ThaumicMekanism/ChemE-Car-Electrical-Team-2018-2019/Box/Images/analog digital.jpg

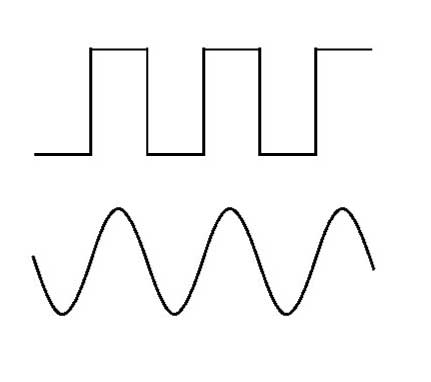
Box/Images/analog digital.jpg
