ThaumicMekanism/ChemE-Car-Electrical-Team-2018-2019/Box/Images/brain.jpg

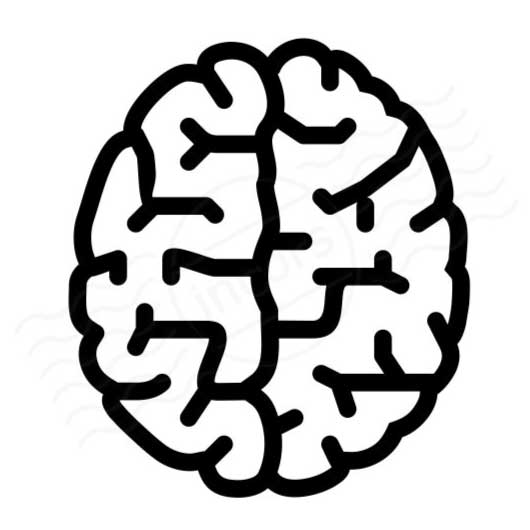
Box/Images/brain.jpg
