ThaumicMekanism/ChemE-Car-Electrical-Team-2018-2019/New Motor Control/proj-bjt.png

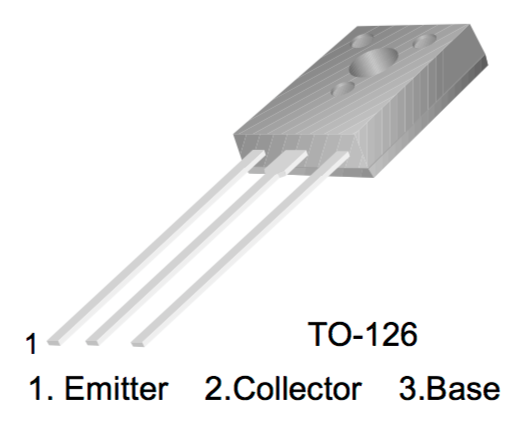
New Motor Control/proj-bjt.png
