ThaumicMekanism/ChemE-Car-Electrical-Team-2018-2019/New Motor Control/proj-motor-driver.png

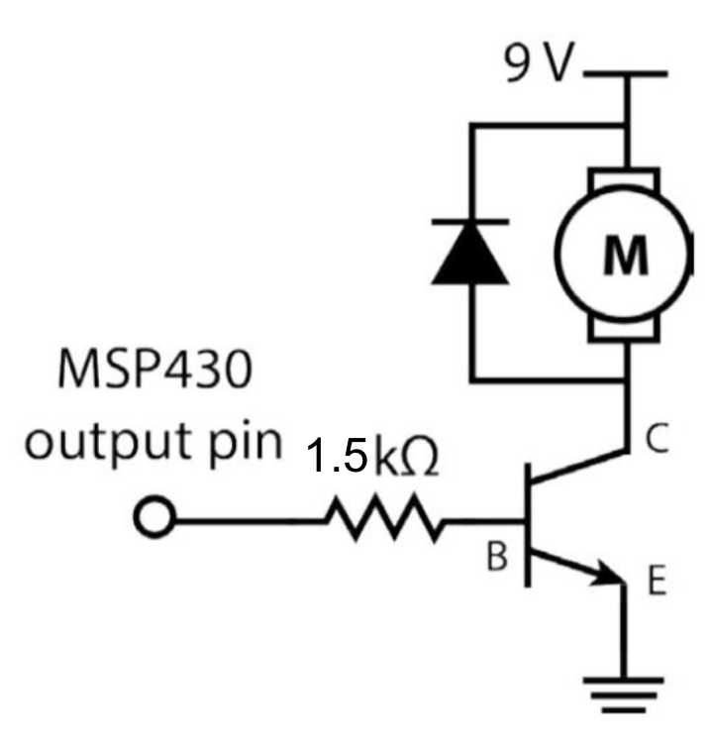
New Motor Control/proj-motor-driver.png
