ThaumicMekanism/ChemE-Car-Electrical-Team-2018-2019/motor_control/debug.h

#ifndef debug_h
#define debug_h
/* These variables are for debug purposes, for the command line outputs. */

//Prints the value of the 'state' variable.
#define debug_state false
//Prints the value of the 'on' variable
#define debug_on false
//Prints every time the board does a check;
#define debug_check false
//Allows the board_ready pin to activate (turn on the led)
#define debug_board_ready true
//Allows the board_error pin to activate (turn on the led)
#define debug_board_error false

#endif
