ThaumicMekanism/ChemE-Car-Electrical-Team-2018-2019/motor_control/Led.h

#ifndef Led_h
#define Led_h

class Led {
  public:
    int pin;
    unsigned long duration;
    int numBlinks;
    long offset;
    unsigned long prevTime;
    bool state;
    Led(int _pin, bool state, unsigned long _duration, int _numBlinks, long _offset);
};

Led::Led(int _pin, bool _state, unsigned long _duration, int _numBlinks, long _offset) {
    pin = _pin;
    duration = _duration;
    numBlinks = _numBlinks;
    offset = _offset;
    state = _state;
    prevTime = millis();
}

#endif
